platima/PCBWay-11th-Design-Contest/Hardware/KiCad Files/Models/STM8S003F3P6.stp

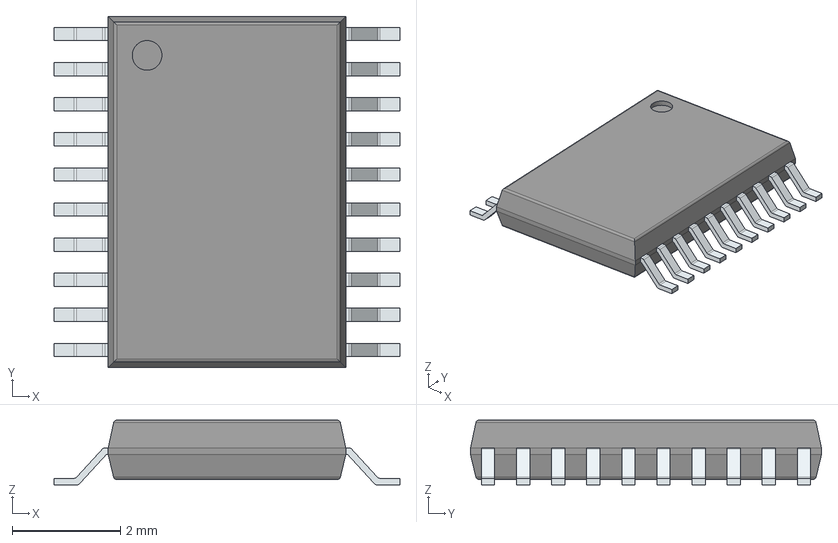
[picture p18: CAD file, 2025-06-13]
Hardware/KiCad Files/Models/STM8S003F3P6.stp
6.40 x 6.50 x 1.20 mm
PinsArrayLR
