platima/PCBWay-11th-Design-Contest/Firmware/ws2812_stm8s.h

/*
 * Copyright (C) 2022  Patrick Pedersen

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
 */

/**
 * @file ws2812_stm8s.h
 * @author Patrick Pedersen
 * @date 2022-10-26
 * 
 * @brief Provides STM8S platform specific definitions.
 * 
 */

#pragma once

#define WS2812_TARGET_PLATFORM_STM8S // 2025-05-21 Platima: Added due to how Arduino compiles - not defined at build time
#ifdef WS2812_TARGET_PLATFORM_STM8S

#include <stm8s.h>
#include <stdint.h>

#include "ws2812_common.h" // 2025-05-21 Platima: Changed to "";s due to local include

// General description necessary for Doxygen

/** @brief ALL PLATFORMS: Data structure to configure a @ref ws2812 "WS2812 device struct"
 * 
 * The following struct is used to initialize/configure a @ref ws2812 "WS2812 device struct"
 * It is passed to the ws2812_config() function along with a reference to a @ref ws2812 
 * "WS2812 device struct", and contains relevant information such as pins used to drive WS2812 devices,
 * the device's reset time etc.
 * 
 * This struct vareies between platforms, and is defined in the platform specific header file (`ws2812_PLATFORM.h`).
 * 
 * @warning All fields of the configuration object must be defined before passing it to #ws2812_config()!
 *          Leaving a field undefined will result in undefined behaivor!
 */

/*
 * STM8: Data structure to configure a @ref ws2812 "WS2812 device struct" on STM8S platforms.
 * 
 * The following struct is used to initialize/configure a @ref ws2812 "WS2812 device struct"
 * on STM8S based devices. It is passed to the ws2812_config() function along
 * with a reference to a @ref ws2812 "WS2812 device struct", and contains relevant
 * information such as pins used to drive WS2812 devices, the device's reset time etc., 
 * necessary for configuring the @ref ws2812 "WS2812 device struct" to drive one or multiple 
 * WS2812 devices on STM8S based devices.
 * 
 * NOTE: The library currently makes use of the STM8 Standard Peripheral Library meaning it is
 * a required dependency to use this library.
 * 
 * WARNING: All fields of the configuration object must be defined before passing it to #ws2812_config()!
 *      Leaving a field undefined will result in undefined behaivor!
 */
typedef struct ws2812_cfg {
	uint16_t port_baseaddr; ///< Base address of the port used to drive WS2812 devices (ex. GPIOA_BASE, GPIOB_BASE, etc...)
        GPIO_Pin_TypeDef *pins; ///< Array of pins used to drive WS2812 devices (ex. GPIO_PIN_1, GPIO_PIN_2, etc...)
        uint8_t rst_time_us;    ///< Time required for the WS2812 device(s) to reset in us
        ws2812_order order;     ///< Color order of the WS2812 device(s) (ex. rgb, grb, bgr...)
        uint8_t n_dev;          ///< Number of WS2812 devices to drive
} ws2812_cfg;

// General description necessary for Doxygen

/**
 * @brief ALL PLATFORMS: WS2812 device struct to drive one or more WS2812 devices.
 * 
 * The following struct is used to drive one or more WS2812 devices.
 * It is initialized by the ws2812_config() function and is taken as an argument by practically
 * every function of the TinyWS2812 library relevant to driving WS2812 devices (ex. ws2812_tx(),
 * ws2812_prep_tx(), etc...).
 * 
 * @see ws2812_config()
 * 
 */

/*
 * WS2812 device struct to drive one or more WS2812 devices on STM8S based platforms.
 * 
 * The following struct is used to drive one or more WS2812 devices on STM8S based devices.
 * It is initialized by the ws2812_config() function and is taken as an argument by practically
 * every function of the TinyWS2812 library relevant to driving WS2812 devices (ex. ws2812_tx(),
 * ws2812_prep_tx(), etc...).
 * 
 * See ws2812_config()
 * 
 */
typedef struct ws2812 {
        uint16_t port_baseaddr; ///< Base address of the port used to drive WS2812 devices (ex. GPIOA_BASE, GPIOB_BASE, etc...)
        uint8_t rst_time_us;    ///< Time required for WS2812 to reset in us
        uint8_t maskhi;         ///< PORT masks to toggle the data pins high.
        uint8_t masklo;         ///< PORT masks to toggle the data pins low.
        uint8_t rgbmap[3];      ///< RGB map to map/convert RGB values to another color order
} ws2812;

#endif
