platima/PCBWay-11th-Design-Contest/Firmware/ws2812_common.h

/*
 * Copyright (C) 2021  Patrick Pedersen

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
 */

/**
 * @file ws2812_common.h
 * @author Patrick Pedersen
 * @date 2021-04-16
 * 
 * @brief Definitions required by all platform specific headers.
 * 
 * The following header features platform independent definitions,
 * such as typedefs, enums and structs, that are used across
 * all platorm specific headers.
 * 
 */

#pragma once

/**
 * @brief Enum to specify the WS2812 device's color order.
 *
 * Unfortunately there is no clear standard on sequential color
 * order of WS2812 LEDs, some are intuitively programmed in
 * RGB order, however, many, if not the majority, are programmed
 * in GRB oder. As there is automatic way to identify the correct
 * color order, it must be manually provided in the device configuration
 * with this enum.
 */
typedef enum {
        rgb,
        rbg,
        brg,
        bgr,
        grb,
        gbr
} ws2812_order;

#ifndef __SDCC // 2025-05-21 Platima: SDCC packs structures by default on 8-bit processors 
#pragma pack(1)
#endif
/**
 * @brief Data structure to hold RGB color values.
 *
 * The RGB struct holds the red, green and blue values
 * to define colors. It is used by the ws2812_tx() function 
 * to set the color of one or more WS2812 LEDs.
 * 
 * @note It should be noted that WS2812 LEDs typically suffer
 *      from poor color accuracy. As an example, the typical RGB
 *      value for orange (255,165,0) displays a color closer to 
 *      yellow on my WS2812 strip.  
 *
 */
typedef struct ws2812_rgb {
        uint8_t r,g,b;
} ws2812_rgb;

void _ws2812_get_rgbmap(uint8_t (*rgbmap)[3], ws2812_order order);
